alvaroalea/QL_mIce_Starmouse/QL_mIce_Starmouse.kicad_sch

## KiCad design QL_mIce_Starmouse.kicad_sch (2024-07-19)

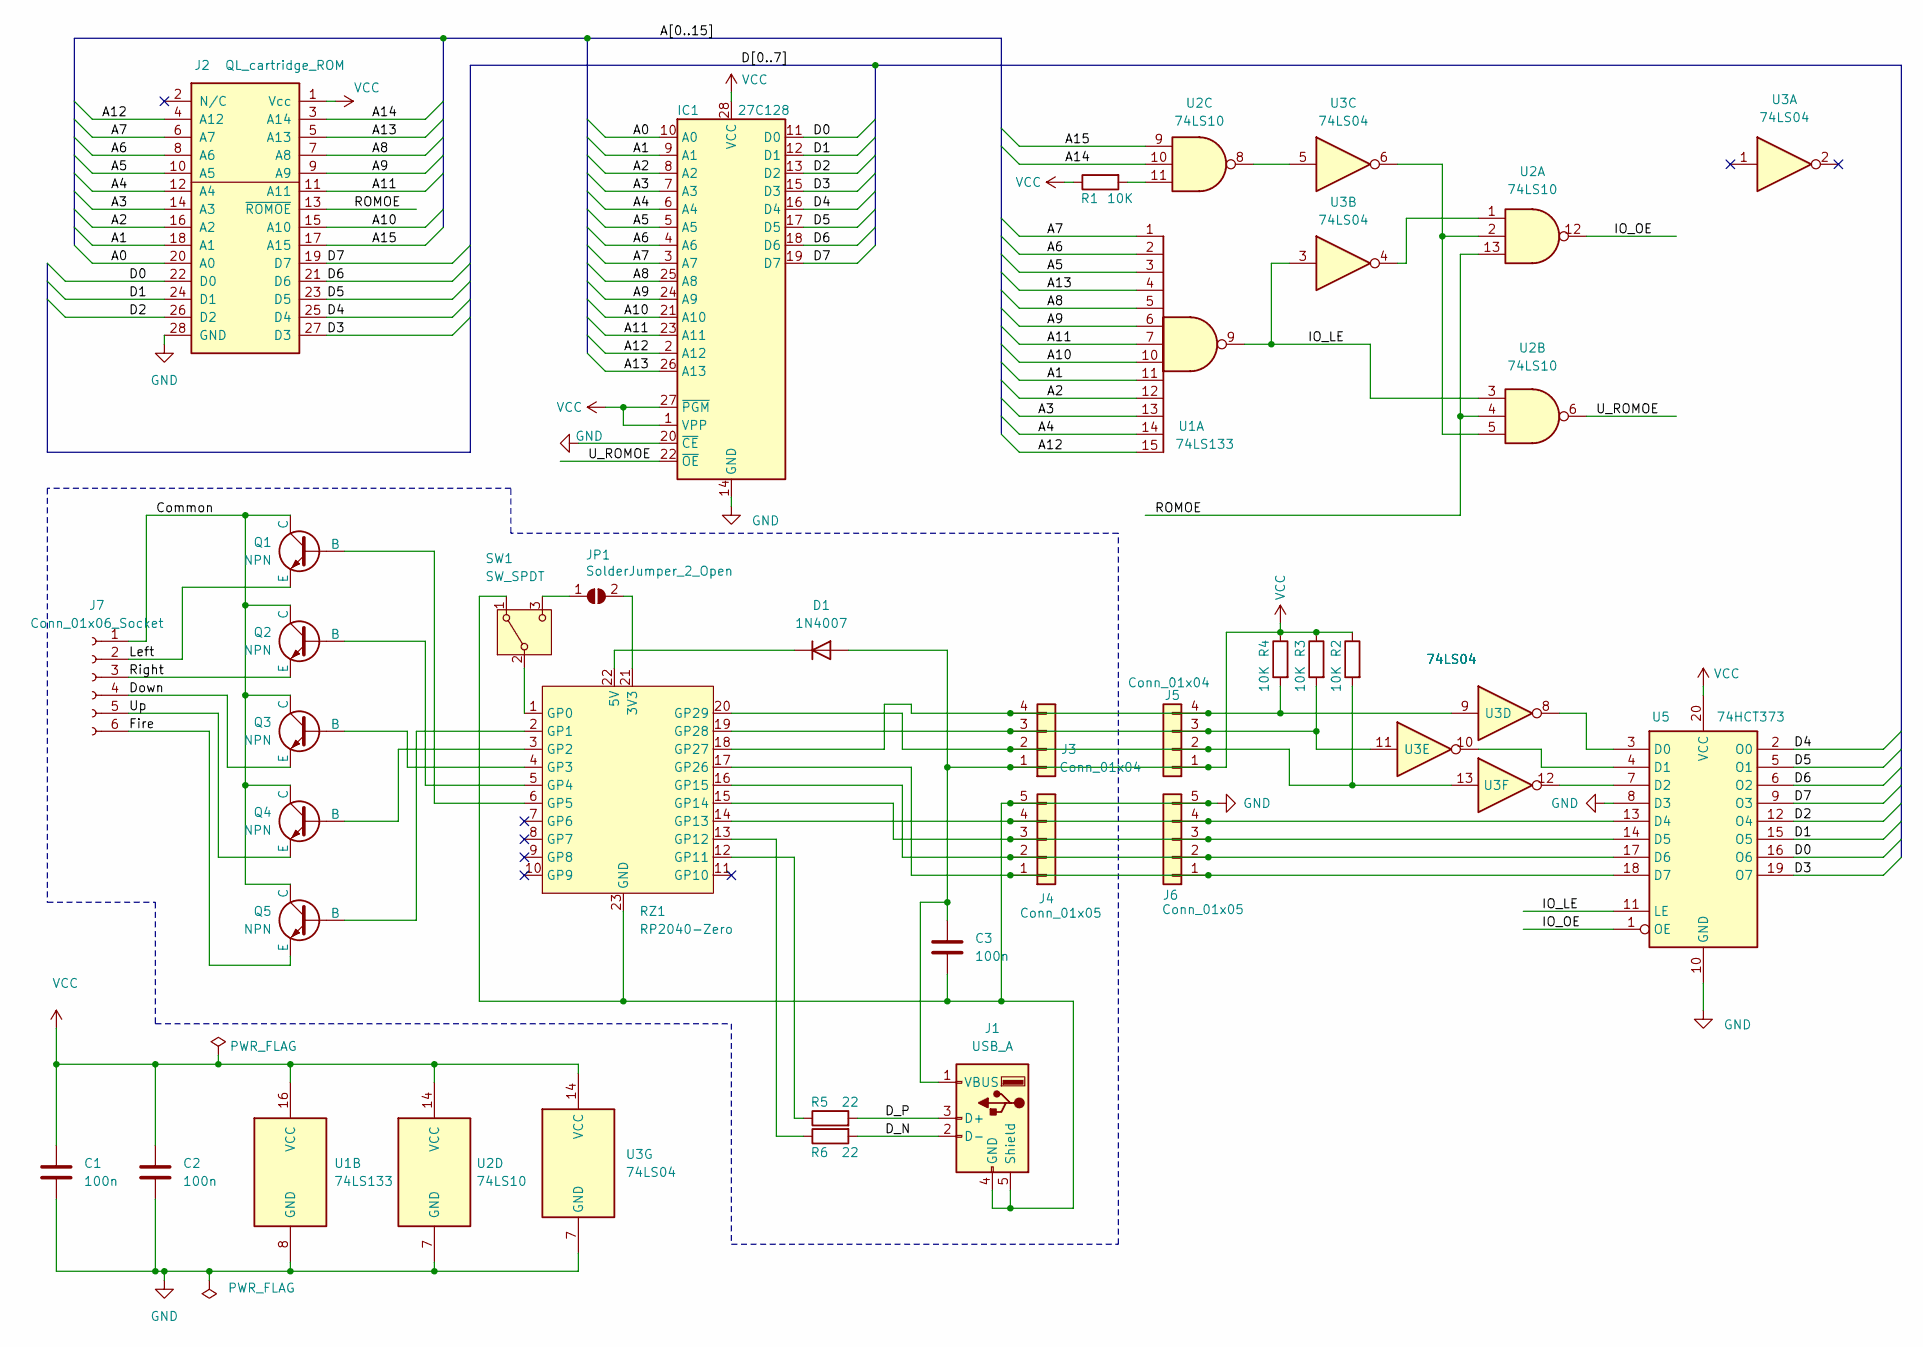
[picture p14: schematic QL_mIce_Starmouse.kicad_sch]

Parts:
C1, C2, C3: 100n; C_Disc_D5.0mm_W2.5mm_P5.00mm
D1: 1N4007; D_DO-41_SOD81_P10.16mm_Horizontal
IC1: 27C128; DIP-28_W15.24mm_LongPads
J1: USB_A; USB_A_Molex_67643_Horizontal
J2: QL_cartridge_ROM; CART_QL_EDGE
J3: Conn_01x04; PinHeader_1x04_P2.54mm_Vertical
J4: Conn_01x05; PinHeader_1x05_P2.54mm_Vertical
J5: Conn_01x04; PinSocket_1x04_P2.54mm_Vertical
J6: Conn_01x05; PinSocket_1x05_P2.54mm_Vertical
J7: Conn_01x06_Socket; Molex_KK-254_AE-6410-06A_1x06_P2.54mm_Vertical
JP1: SolderJumper_2_Open; SolderJumper-2_P1.3mm_Open_RoundedPad1.0x1.5mm
Q1, Q2, Q3, Q4, Q5: NPN; TO-92
R1, R2, R3, R4: 10K; R_Axial_DIN0207_L6.3mm_D2.5mm_P7.62mm_Horizontal
R5, R6: 22; R_Axial_DIN0207_L6.3mm_D2.5mm_P7.62mm_Horizontal
RZ1: RP2040-Zero
SW1: SW_SPDT; PinHeader_1x03_P2.54mm_Vertical
U1: 74LS133; DIP-16_W7.62mm_LongPads
U2: 74LS10; DIP-14_W7.62mm_LongPads
U3: 74LS04; DIP-14_W7.62mm_LongPads
U5: 74HCT373; DIP-20_W7.62mm_LongPads

Connections:
A0: IC1.10 (A0), J2.20 (A0)
A1: IC1.9 (A1), J2.18 (A1), U1.11
A2: IC1.8 (A2), J2.16 (A2), U1.12
A3: IC1.7 (A3), J2.14 (A3), U1.13
A4: IC1.6 (A4), J2.12 (A4), U1.14
A5: IC1.5 (A5), J2.10 (A5), U1.3
A6: IC1.4 (A6), J2.8 (A6), U1.2
A7: IC1.3 (A7), J2.6 (A7), U1.1
A8: IC1.25 (A8), J2.7 (A8), U1.5
A9: IC1.24 (A9), J2.9 (A9), U1.6
A10: IC1.21 (A10), J2.15 (A10), U1.10
A11: IC1.23 (A11), J2.11 (A11), U1.7
A12: IC1.2 (A12), J2.4 (A12), U1.15
A13: IC1.26 (A13), J2.5 (A13), U1.4
A14: J2.3 (A14), U2.10
A15: J2.17 (A15), U2.9
Common: J7.1, Q1.1 (C), Q2.1 (C), Q3.1 (C), Q4.1 (C), Q5.1 (C)
D0: IC1.11 (D0), J2.22 (D0), U5.16 (O6)
D1: IC1.12 (D1), J2.24 (D1), U5.15 (O5)
D2: IC1.13 (D2), J2.26 (D2), U5.12 (O4)
D3: IC1.15 (D3), J2.27 (D3), U5.19 (O7)
D4: IC1.16 (D4), J2.25 (D4), U5.2 (O0)
D5: IC1.17 (D5), J2.23 (D5), U5.5 (O1)
D6: IC1.18 (D6), J2.21 (D6), U5.6 (O2)
D7: IC1.19 (D7), J2.19 (D7), U5.9 (O3)
D_N: J1.2 (D-), R6.2
D_P: J1.3 (D+), R5.2
Down: J7.4, Q3.3 (E)
Fire: J7.6, Q5.3 (E)
GND: C1.2, C2.2, C3.2, IC1.14 (GND), IC1.20 (~CE), J1.4 (GND), J1.5 (Shield), J2.28 (GND), J4.5, J6.5, RZ1.23 (GND), SW1.1 (A), U1.8 (GND), U2.7 (GND), U3.7 (GND), U5.8 (D3), U5.10 (GND)
IO_LE: U1.9, U2.3, U3.3, U5.11 (LE)
IO_OE: U2.12, U5.1 (OE)
Left: J7.2, Q1.3 (E)
unnamed: D1.1 (K), RZ1.22 (5V)
unnamed: J3.2, J5.2, R2.2, RZ1.20 (GP29), U3.13
unnamed: J3.3, J5.3, R3.2, RZ1.19 (GP28), U3.11
unnamed: J3.4, J5.4, R4.2, RZ1.18 (GP27), U3.9
unnamed: J4.1, J6.1, RZ1.17 (GP26), U5.18 (D7)
unnamed: J4.2, J6.2, RZ1.16 (GP15), U5.17 (D6)
unnamed: J4.3, J6.3, RZ1.15 (GP14), U5.14 (D5)
unnamed: J4.4, J6.4, RZ1.14 (GP13), U5.13 (D4)
unnamed: JP1.1 (A), SW1.3 (C)
unnamed: JP1.2 (B), RZ1.21 (3V3)
unnamed: Q1.2 (B), RZ1.6 (GP5)
unnamed: Q2.2 (B), RZ1.5 (GP4)
unnamed: Q3.2 (B), RZ1.4 (GP3)
unnamed: Q4.2 (B), RZ1.3 (GP2)
unnamed: Q5.2 (B), RZ1.2 (GP1)
unnamed: R1.2, U2.11
unnamed: R5.1, RZ1.12 (GP11)
unnamed: R6.1, RZ1.13 (GP12)
unnamed: RZ1.1 (GP0), SW1.2 (B)
unnamed: U2.1, U3.4
unnamed: U2.2, U2.5, U3.6
unnamed: U2.8, U3.5
unnamed: U3.8, U5.3 (D0)
unnamed: U3.10, U5.4 (D1)
unnamed: U3.12, U5.7 (D2)
ROMOE: J2.13 (~ROMOE), U2.4, U2.13
Right: J7.3, Q2.3 (E)
U_ROMOE: IC1.22 (~OE), U2.6
Up: J7.5, Q4.3 (E)
VCC: C1.1, C2.1, C3.1, D1.2 (A), IC1.1 (VPP), IC1.27 (~PGM), IC1.28 (VCC), J1.1 (VBUS), J2.1 (Vcc), J3.1, J5.1, R1.1, R2.1, R3.1, R4.1, U1.16 (VCC), U2.14 (VCC), U3.14 (VCC), U5.20 (VCC)
